Xinyuan-LilyGO/T-CAN485/image/6.png

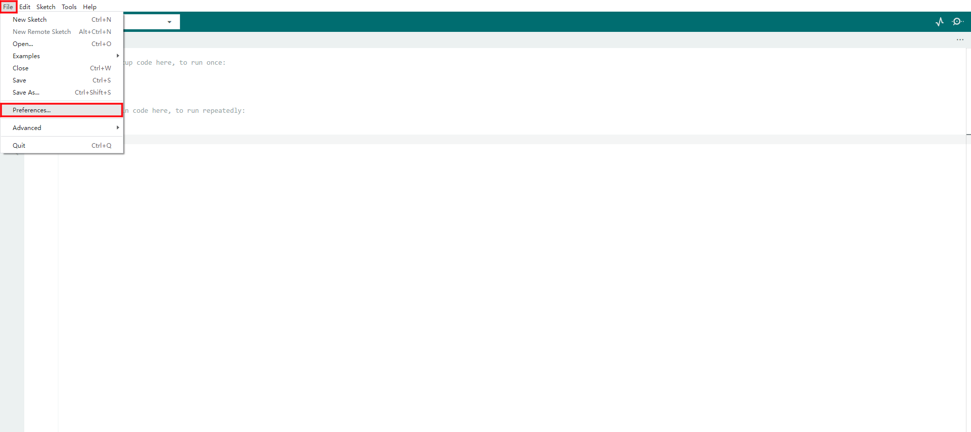
image/6.png
