Xinyuan-LilyGO/T-CAN485/image/7.png

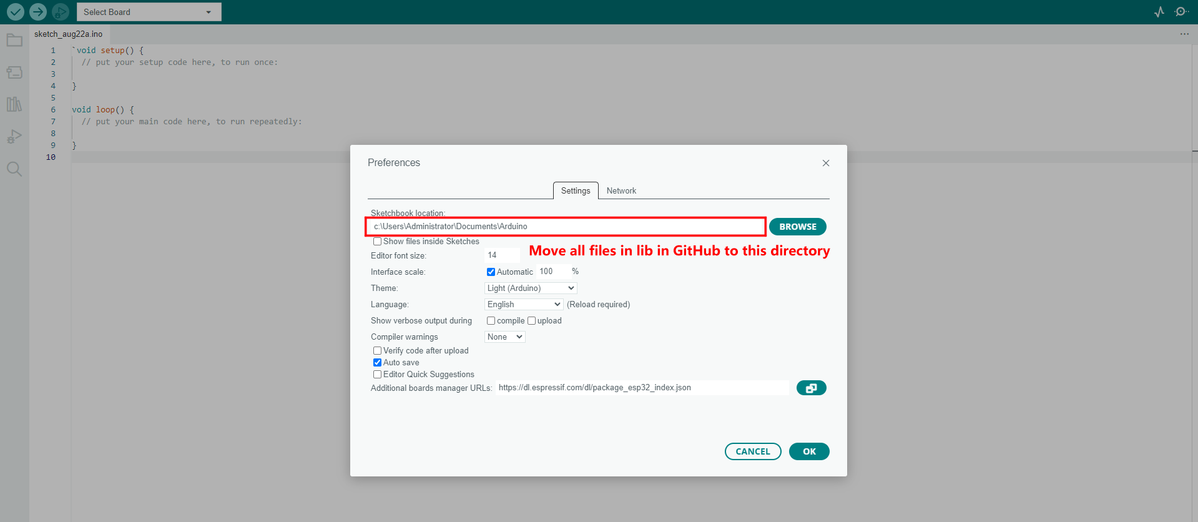
image/7.png
